rogermiranda1000/Domotica/apertura/diagrama.png

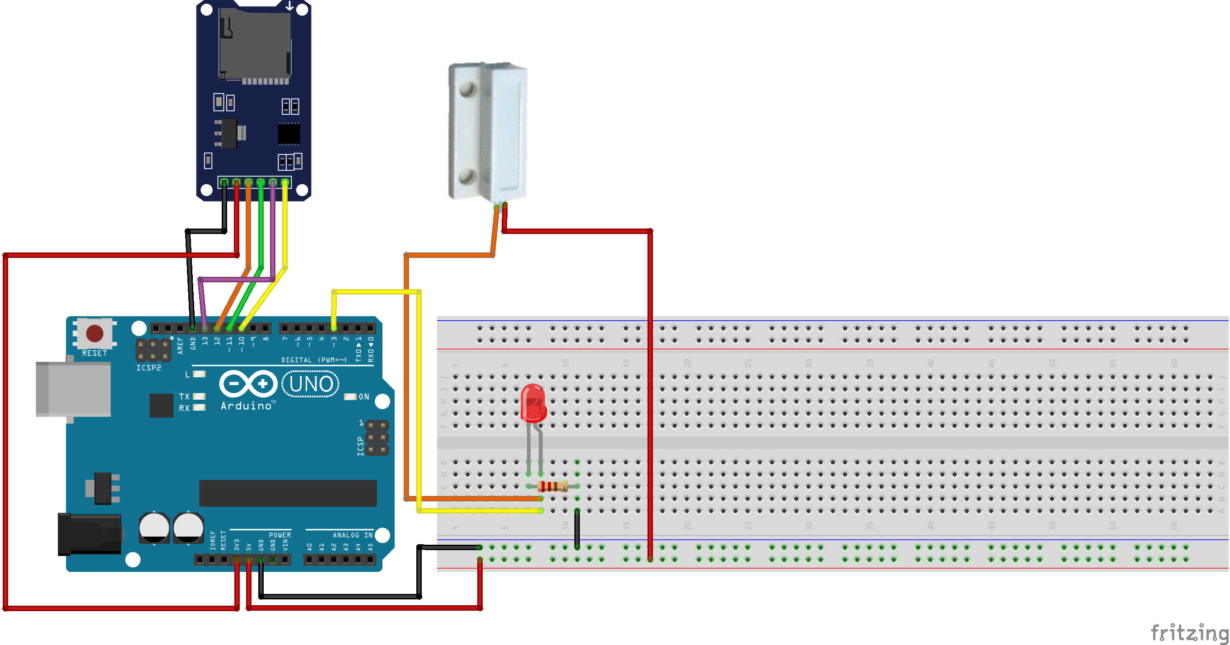
apertura/diagrama.png
