rogermiranda1000/Domotica/enchufe/diagrama.png

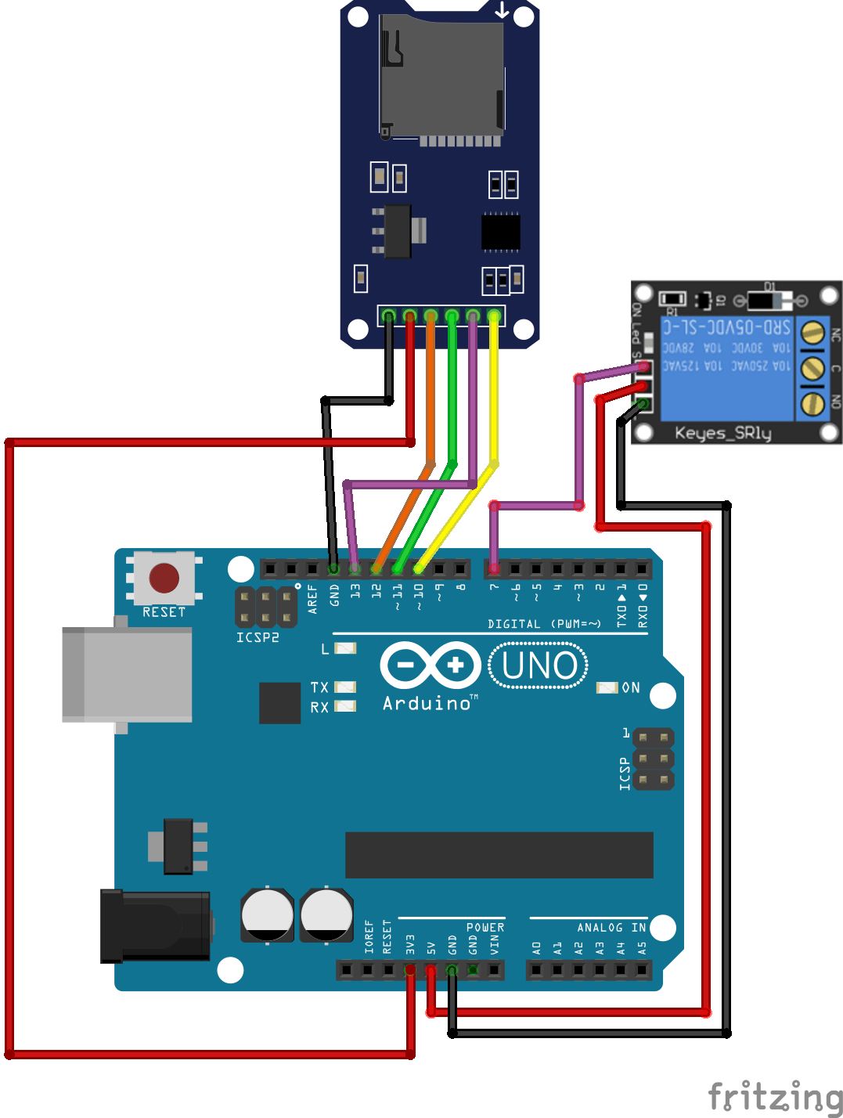
enchufe/diagrama.png
