rogermiranda1000/Domotica/movimiento/diagrama.PNG

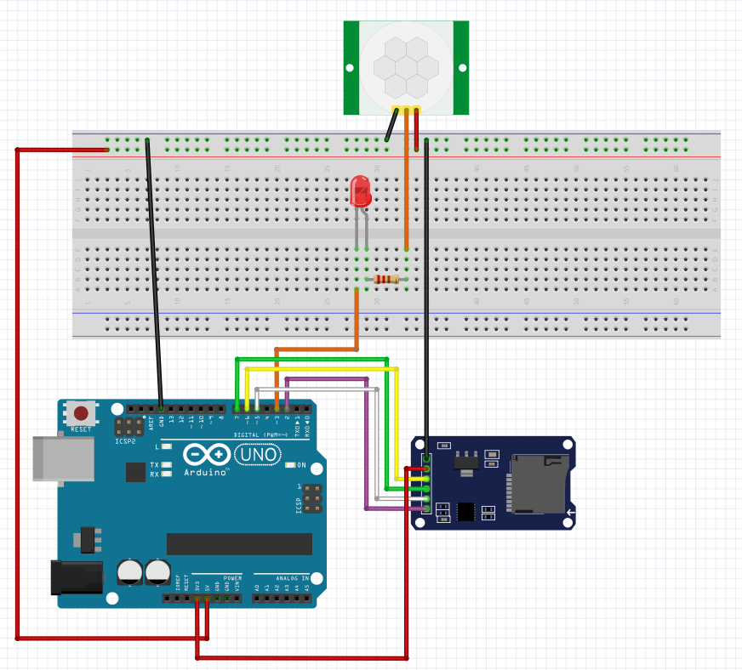
movimiento/diagrama.PNG
